ThanosPapad/dev_buddy/dev_buddy_v1/inc/uart_coms.h

/** @file uart_coms.h
 * 
 * @brief Global information used and visible by all files
 *
 * @par       
 * COPYRIGHT NOTICE: (c) TP Industries Group.  All rights reserved.
 */ 

#ifndef UART_COMS
#define UART_COMS
#include <stdint.h>
#include "pico/unique_id.h"
#include "hardware/uart.h"
#include "hardware/dma.h"
#include "in_out_ctrl.h"

#define UART_ID uart0
#define BAUD_RATE 250000
#define UART_TX_PIN 0
#define UART_RX_PIN 1

#define RX_MAX_LEN 113

#define RX_BUF_SIZE         256
#define RX_BUF_MASK         (RX_BUF_SIZE - 1)

typedef enum
{
    SET_ADC_INTERVAL_REQ = 11,
    SET_ADC_INTERVAL_RESP = 12,
    SET_ADC_INTERVAL_STATE_REQ = 13,
    SET_ADC_INTERVAL_STATE_RESP = 14,
    SET_DEVICE_OUTPUTS = 21,
    GET_DEVICE_OUTPUTS_REQ = 22,
    GET_DEVICE_OUTPUTS_RESP = 23,
    SET_DAC_VALUE_REQ = 31,
    SET_DAC_VALUE_RESP = 32,
    ADC_TELEMETRY_TRANS = 102,
    INCOMING_HANDSHKE_REQ = 111,
    OUTGOING_HANDSHAKE_REQ = 112,
    PIO_UART_CH0_TRANS = 113,
    PIO_UART_CH0_REC = 114,
    PIO_UART_CH1_TRANS = 115,
    PIO_UART_CH1_REC = 116,
    PIO_UART_CH2_TRANS = 117,
    PIO_UART_CH2_REC = 118
} packet_type_t;

typedef enum
{
    IDLE_CONNECTION,
    COM_CONNECTED,
    COM_BUSY,
    COM_FULL,
    COM_FULL_CONFIRMCON

} connection_status_t;

typedef struct __attribute__((packed))
{
    uint8_t chip_id[8];
    uint8_t  handshake_value;
    uint8_t device_number;
    uint8_t data[100];
    uint16_t payload_length;

} handshake_packet_t;

extern connection_status_t conn_stat;
extern bool set_dac_flag;
extern volatile bool usb_active;
// void handle_uart_rcv();

void uart_dma_write(const uint8_t *data, size_t len);
void process_rx_dma(void);
void serial_init(void);
void handle_uart_rcv(void);
void transmit_adc_meas();
void feed_usb_rx(void);
void transmit_pio_uart_channels(void);

#endif
