ThanosPapad/dev_buddy/dev_buddy_v1/inc/tusb_config.h

#ifndef TUSB_CONFIG_H
#define TUSB_CONFIG_H

#define CFG_TUSB_RHPORT0_MODE     OPT_MODE_DEVICE
// #define CFG_TUSB_OS               OPT_OS_NONE

#define CFG_TUD_CDC               1
#define CFG_TUD_MSC               0
#define CFG_TUD_HID               0
#define CFG_TUD_MIDI              0
#define CFG_TUD_VENDOR            0

#define CFG_TUD_CDC_RX_BUFSIZE    256
#define CFG_TUD_CDC_TX_BUFSIZE    256
#define CFG_TUD_CDC_EP_BUFSIZE    64

#endif
