ThanosPapad/dev_buddy/dev_buddy_v1/inc/globals.h

/** @file globals.h
 * 
 * @brief Global information used and visible by all files
 *
 * @par       
 * COPYRIGHT NOTICE: (c) TP Industries Group.  All rights reserved.
 */ 

#ifndef MODULE_H
#define MODULE_H

#include "pico/stdlib.h"


//------ DEFINES START--------

// Uncomment this when ready to test outputs.
// #define OUTPUTS_READY

//------ DEFINES END--------

#endif /* MODULE_H */
